Nixxye/AirBand/Firmware2/src/Gyroscope.cpp

#include "../include/Gyroscope.hpp"
#include "driver/timer.h"
#include "Arduino.h"

// << REMOVIDO >> A variável de interrupção não é mais necessária.
// volatile bool mpuInterrupt = false;

Gyroscope* Gyroscope::instance = nullptr;
Gyroscope::Gyroscope() : initSuccess(0), AcX(0), AcY(0), AcZ(0), Tmp(0), GyX(0), GyY(0), GyZ(0)
{
    Serial.println("|Gyroscope| ------- Iniciando MPU6050 ---------");
    configMPU6050();
    Serial.println("|Gyroscope| -------- MPU6050 iniciado com sucesso! ---------");
}

void Gyroscope::getData(int16_t* ax, int16_t* ay, int16_t* az, int16_t* temp, int16_t* gx, int16_t* gy, int16_t* gz){
    *ax = AcX;
    *ay = AcY;
    *az = AcZ;
    *temp = Tmp;
    *gx = GyX;
    *gy = GyY;
    *gz = GyZ;
}

// ================== FUNÇÃO MODIFICADA ==================
void Gyroscope::loop(){     
    // << MODIFICADO >> A verificação da interrupção foi removida.
    // A leitura e impressão ocorrem a cada chamada desta função.
    readData();

    // Serial.print("AcX: "); Serial.print(AcX / 100.0);
    // Serial.print(" | AcY: "); Serial.print(AcY / 100.0);
    // Serial.print(" | AcZ: "); Serial.print(AcZ / 100.0);
    // Serial.print(" | Tmp: "); Serial.print(Tmp / 100.0);
    // Serial.print(" | GyX: "); Serial.print(GyX / 100.0);
    // Serial.print(" | GyY: "); Serial.print(GyY / 100.0);
    // Serial.print(" | GyZ: "); Serial.println(GyZ / 100.0);
}
// ========================================================

void Gyroscope::readData()
{
    Wire.beginTransmission(MPU_ADDR);
    Wire.write(0x3B);  // primeiro registrador de dados (AcX)
    Wire.endTransmission(false);
    Wire.requestFrom(MPU_ADDR, 14, 1);  // pede 14 bytes de uma vez

    AcX = Wire.read() << 8 | Wire.read();
    AcY = Wire.read() << 8 | Wire.read();
    AcZ = Wire.read() << 8 | Wire.read();
    Tmp = Wire.read() << 8 | Wire.read();
    GyX = Wire.read() << 8 | Wire.read();
    GyY = Wire.read() << 8 | Wire.read();
    GyZ = Wire.read() << 8 | Wire.read();

    // Atualiza valores com valores fisicos
    AcX = (int16_t) ((AcX / ACCEL_SCALE) * 100);
    AcY = (int16_t) ((AcY / ACCEL_SCALE) * 100);
    AcZ = (int16_t) ((AcZ / ACCEL_SCALE) * 100);
    Tmp = (int16_t) ((Tmp / 340.0 + 36.53) * 100);
    GyX = (int16_t) ((GyX / GYRO_SCALE) * 100);
    GyY = (int16_t) ((GyY / GYRO_SCALE) * 100);
    GyZ = (int16_t) ((GyZ / GYRO_SCALE) * 100);
}

void Gyroscope::configMPU6050(){
    initSuccess = 1;
    uint8_t resultDebug = 0;
    // Acorda o MPU6050
    Serial.println("|Gyroscope| - Acordando o MPU6050...");
    Wire.beginTransmission(MPU_ADDR);
    Wire.write(0x6B);      //registrador PWR_MGMT_1
    Wire.write(0x00);      // coloca em 0 → acorda o sensor
    resultDebug = Wire.endTransmission(true);
    vTaskDelay(5);
    if (resultDebug != 0) {
        Serial.print("|Gyroscope| - Erro ao acordar MPU6050! Código: ");
        Serial.println(resultDebug);
        initSuccess = 0;
    } else {
        Serial.println("|Gyroscope| - MPU6050 acordado!");
    }

    // << REMOVIDO >> A configuração de interrupção foi retirada.
    /*
    // Habilita interrupção de "data ready" no MPU6050
    Serial.println("|Gyroscope| - Configurando interrupção do MPU6050...");
    Wire.beginTransmission(MPU_ADDR);
    Wire.write(0x38);   // registrador INT_ENABLE
    Wire.write(0x01);   // bit 0: DATA_RDY_EN
    resultDebug = Wire.endTransmission(true);
    vTaskDelay(5);
    if (resultDebug != 0) {
        Serial.print("|Gyroscope| - Erro ao configurar interrupção do MPU6050! Código: ");
        Serial.println(resultDebug);
        initSuccess = 0;
    } else {
        Serial.println("|Gyroscope| - Interrupção do MPU6050 configurada!");
    }
    */

    // Configura taxa de trasmisao de dados para 80Hz
    Serial.println("|Gyroscope| - Configurando taxa de transmissão do MPU6050 para 80Hz...");
    Wire.beginTransmission(MPU_ADDR);
    Wire.write(0x19);    // SMPLRT_DIV
    Wire.write(0x63);    // 80Hz
    resultDebug = Wire.endTransmission(true);
    vTaskDelay(5);
    if (resultDebug != 0) {
        Serial.print("|Gyroscope| - Erro ao configurar taxa de transmissão do MPU6050! Código: ");
        Serial.println(resultDebug);
        initSuccess = 0;
    } else {
        Serial.println("|Gyroscope| - Taxa de transmissão do MPU6050 configurada!");
    }

    if (initSuccess) {
        Serial.println("|Gyroscope| - MPU6050 configurado com sucesso!");
    } else {
        Serial.println("|Gyroscope| - Erro na configuração do MPU6050!");
    }
}

Gyroscope::~Gyroscope() {

}

Gyroscope* Gyroscope::Init_Gyroscope() {
    if (instance == nullptr) {
        Serial.println("|Gyroscope| - Iniciando I2C para MPU6050...");
        Wire.begin(PIN_SDA, PIN_SCL);
        vTaskDelay(5);
        Serial.println("|Gyroscope| - I2C iniciado com sucesso!");

        instance = new Gyroscope();
    }
    return instance;
}
