Nixxye/AirBand/Firmware/include/WifiServer.hpp

#ifndef WIFISERVER_HPP
#define WIFISERVER_HPP

#include <WiFi.h>
#include <WiFiUdp.h>
#include <esp_now.h>
#include "Gyroscope.hpp"
#include "Magnetometer.hpp"
#include "AnalogReader.hpp"

#define UDP_PORT 8888
#define WIFI_CHANNEL 1 

// --- ESTRUTURA COMBINADA (Master + Slave) ---
#pragma pack(push, 1)
struct SensorPacket {
    int16_t ax, ay, az;       // Mestra Accel
    int16_t gx, gy, gz;       // Mestra Gyro
    int mx, my, mz;           // Mestra Mag
    float heading;            // Mestra Heading
    float v32, v33, v34, v35; // Mestra ADC
    int16_t slave_ax, slave_ay, slave_az;
    int16_t slave_gx, slave_gy, slave_gz; 
    
    unsigned long timestamp;
} __attribute__((packed));
#pragma pack(pop)

typedef struct slave_msg_t {
  int16_t ax;
  int16_t ay;
  int16_t az;
  int16_t gx;
  int16_t gy;
  int16_t gz;
} slave_msg_t;

class WifiServer {
private:
    static WifiServer* instance;
    WiFiUDP udp;
    const char* ap_ssid;
    const char* ap_password;
    IPAddress pcIP;
    
    // Sensores Locais
    Gyroscope* gyro;
    Magnetometer* mag;
    AnalogReader* adcReader;

    unsigned long lastSendTime;
    
    // Dados voláteis da Escrava (atualizados na interrupção)
    static volatile int16_t rx_ax;
    static volatile int16_t rx_ay;
    static volatile int16_t rx_az;
    static volatile int16_t rx_gx;
    static volatile int16_t rx_gy;
    static volatile int16_t rx_gz;

    WifiServer(const char* ssid, const char* password);

    // Callback estático do ESP-NOW
    static void OnDataRecv(const uint8_t * mac, const uint8_t *incomingData, int len);

public:
    static WifiServer* Init_WifiServer(const char* ssid, const char* password);
    void loop();
    void sendDataToClient();
};

#endif
